qu1j0t3/vector_gen/vector_gen_software/portable/isqrt.c

#include "isqrt.h"

// Square root of integer
// From https://en.wikipedia.org/wiki/Integer_square_root#Example_implementation_in_C

uint32_t isqrt ( uint32_t s )
{
	uint32_t x0 = s / 2;			// Initial estimate
	                        			// Avoid overflow when s is the maximum representable value

	// Sanity check
	if ( x0 != 0 )
	{
		uint32_t x1 = ( x0 + s / x0 ) / 2;	// Update

		while ( x1 < x0 )				// This also checks for cycle
		{
			x0 = x1;
			x1 = ( x0 + s / x0 ) / 2;
		}

		return x0;
	}
	else
	{
		return s;
	}
}
